dhskinner/battery-charge-indicator/design/Solidworks/LED Holder.SLDASM

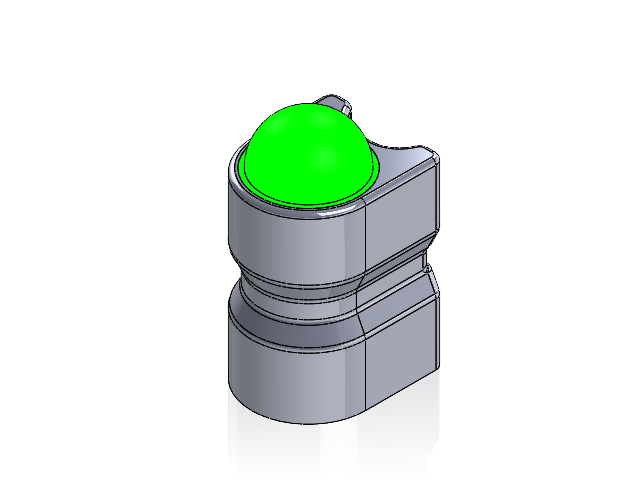
[picture p19: CAD file, 2026-05-02]
design/Solidworks/LED Holder.SLDASM
LED Holder
Big LED
