dhskinner/battery-charge-indicator/design/Solidworks/LED Holder 2.SLDASM

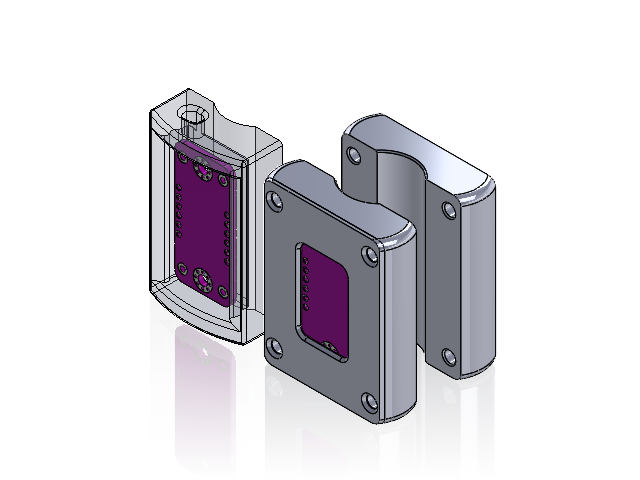
[picture p20: CAD file, 2026-05-02]
design/Solidworks/LED Holder 2.SLDASM
PCB2 x 2
LED Holder 2
LED Holder 3
Part2^LED Holder 2
Part3^LED Holder 2
